michaelkamprath/eater-sap-1-improvements/advanced-alu/schematics/advanced-alu/a-register.kicad_sch

## KiCad design advanced-alu/schematics/advanced-alu/a-register.kicad_sch (2022-05-16)

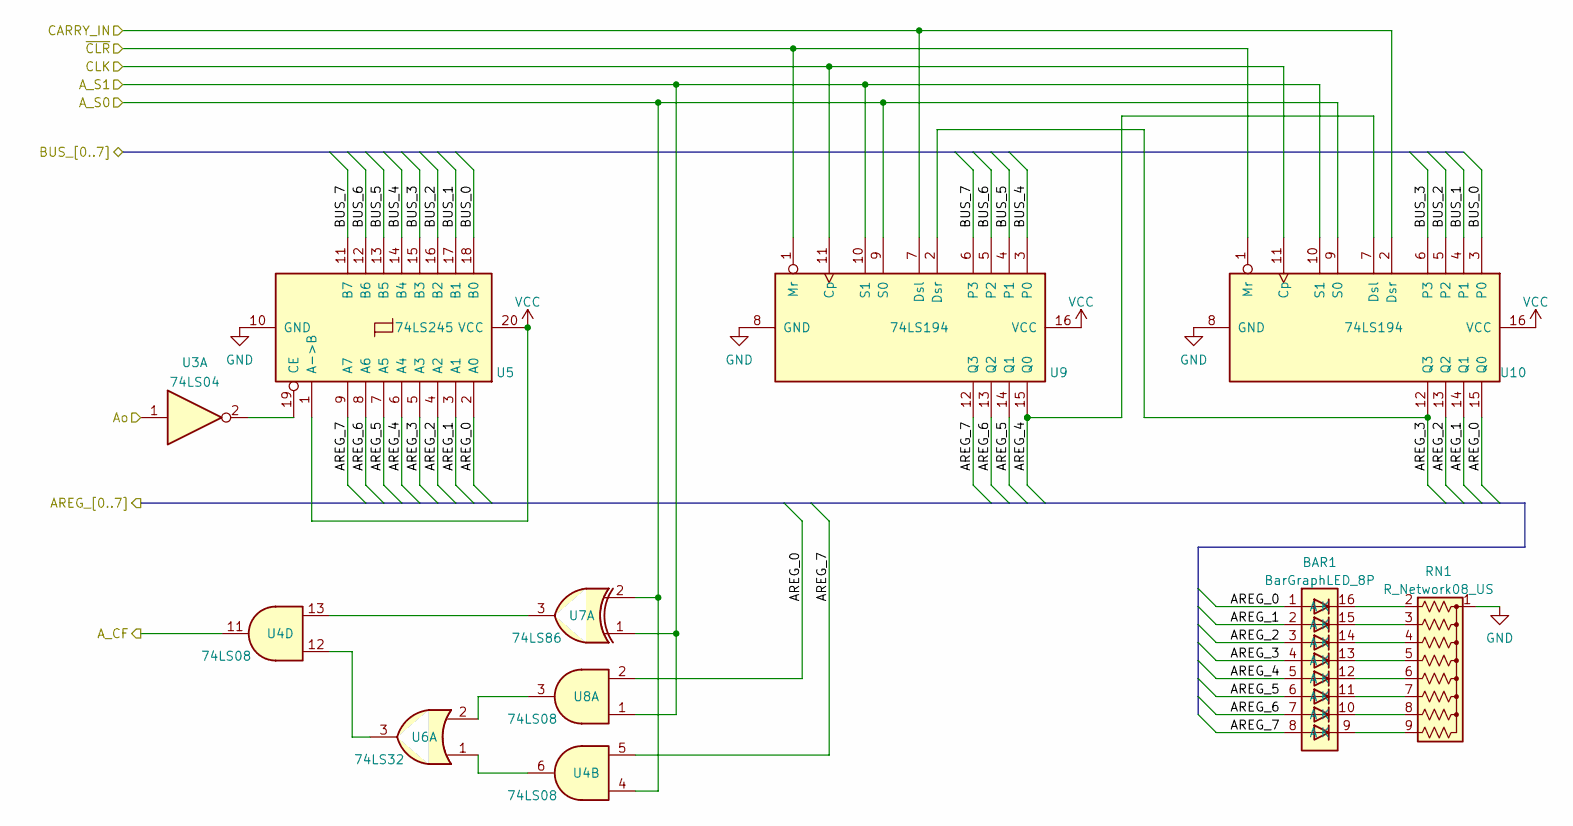
[picture p28: schematic a-register.kicad_sch]

Parts:
BAR1: BarGraphLED_8P
RN1: R_Network08_US; R_Array_SIP9
U3: 74LS04
U4, U8: 74LS08
U5: 74LS245
U6: 74LS32
U7: 74LS86
U9, U10: 74LS194

Connections:
AREG_0: BAR1.1 (A), U5.2 (A0), U8.2, U10.15 (Q0)
AREG_1: BAR1.2 (A), U5.3 (A1), U10.14 (Q1)
AREG_2: BAR1.3 (A), U5.4 (A2), U10.13 (Q2)
AREG_3: BAR1.4 (A), U5.5 (A3), U9.2 (Dsr), U10.12 (Q3)
AREG_4: BAR1.5 (A), U5.6 (A4), U9.15 (Q0), U10.7 (Dsl)
AREG_5: BAR1.6 (A), U5.7 (A5), U9.14 (Q1)
AREG_6: BAR1.7 (A), U5.8 (A6), U9.13 (Q2)
AREG_7: BAR1.8 (A), U4.5, U5.9 (A7), U9.12 (Q3)
A_CF: U4.11
A_S0: U4.4, U7.2, U9.9 (S0), U10.9 (S0)
A_S1: U7.1, U8.1, U9.10 (S1), U10.10 (S1)
Ao: U3.1
BUS_0: U5.18 (B0), U10.3 (P0)
BUS_1: U5.17 (B1), U10.4 (P1)
BUS_2: U5.16 (B2), U10.5 (P2)
BUS_3: U5.15 (B3), U10.6 (P3)
BUS_4: U5.14 (B4), U9.3 (P0)
BUS_5: U5.13 (B5), U9.4 (P1)
BUS_6: U5.12 (B6), U9.5 (P2)
BUS_7: U5.11 (B7), U9.6 (P3)
CARRY_IN: U9.7 (Dsl), U10.2 (Dsr)
CLK: U9.11 (Cp), U10.11 (Cp)
GND: RN1.1 (common), U5.10 (GND), U9.8 (GND), U10.8 (GND)
unnamed: BAR1.9 (K), RN1.9 (R8)
unnamed: BAR1.10 (K), RN1.8 (R7)
unnamed: BAR1.11 (K), RN1.7 (R6)
unnamed: BAR1.12 (K), RN1.6 (R5)
unnamed: BAR1.13 (K), RN1.5 (R4)
unnamed: BAR1.14 (K), RN1.4 (R3)
unnamed: BAR1.15 (K), RN1.3 (R2)
unnamed: BAR1.16 (K), RN1.2 (R1)
unnamed: U3.2, U5.19 (CE)
unnamed: U4.6, U6.1
unnamed: U4.12, U6.3
unnamed: U4.13, U7.3
unnamed: U6.2, U8.3
VCC: U5.1 (A->B), U5.20 (VCC), U9.16 (VCC), U10.16 (VCC)
~CLR: U9.1 (Mr), U10.1 (Mr)
