michaelkamprath/eater-sap-1-improvements/advanced-alu/schematics/advanced-alu/advanced-alu.kicad_sch

## KiCad design advanced-alu/schematics/advanced-alu/advanced-alu.kicad_sch (2022-05-16)

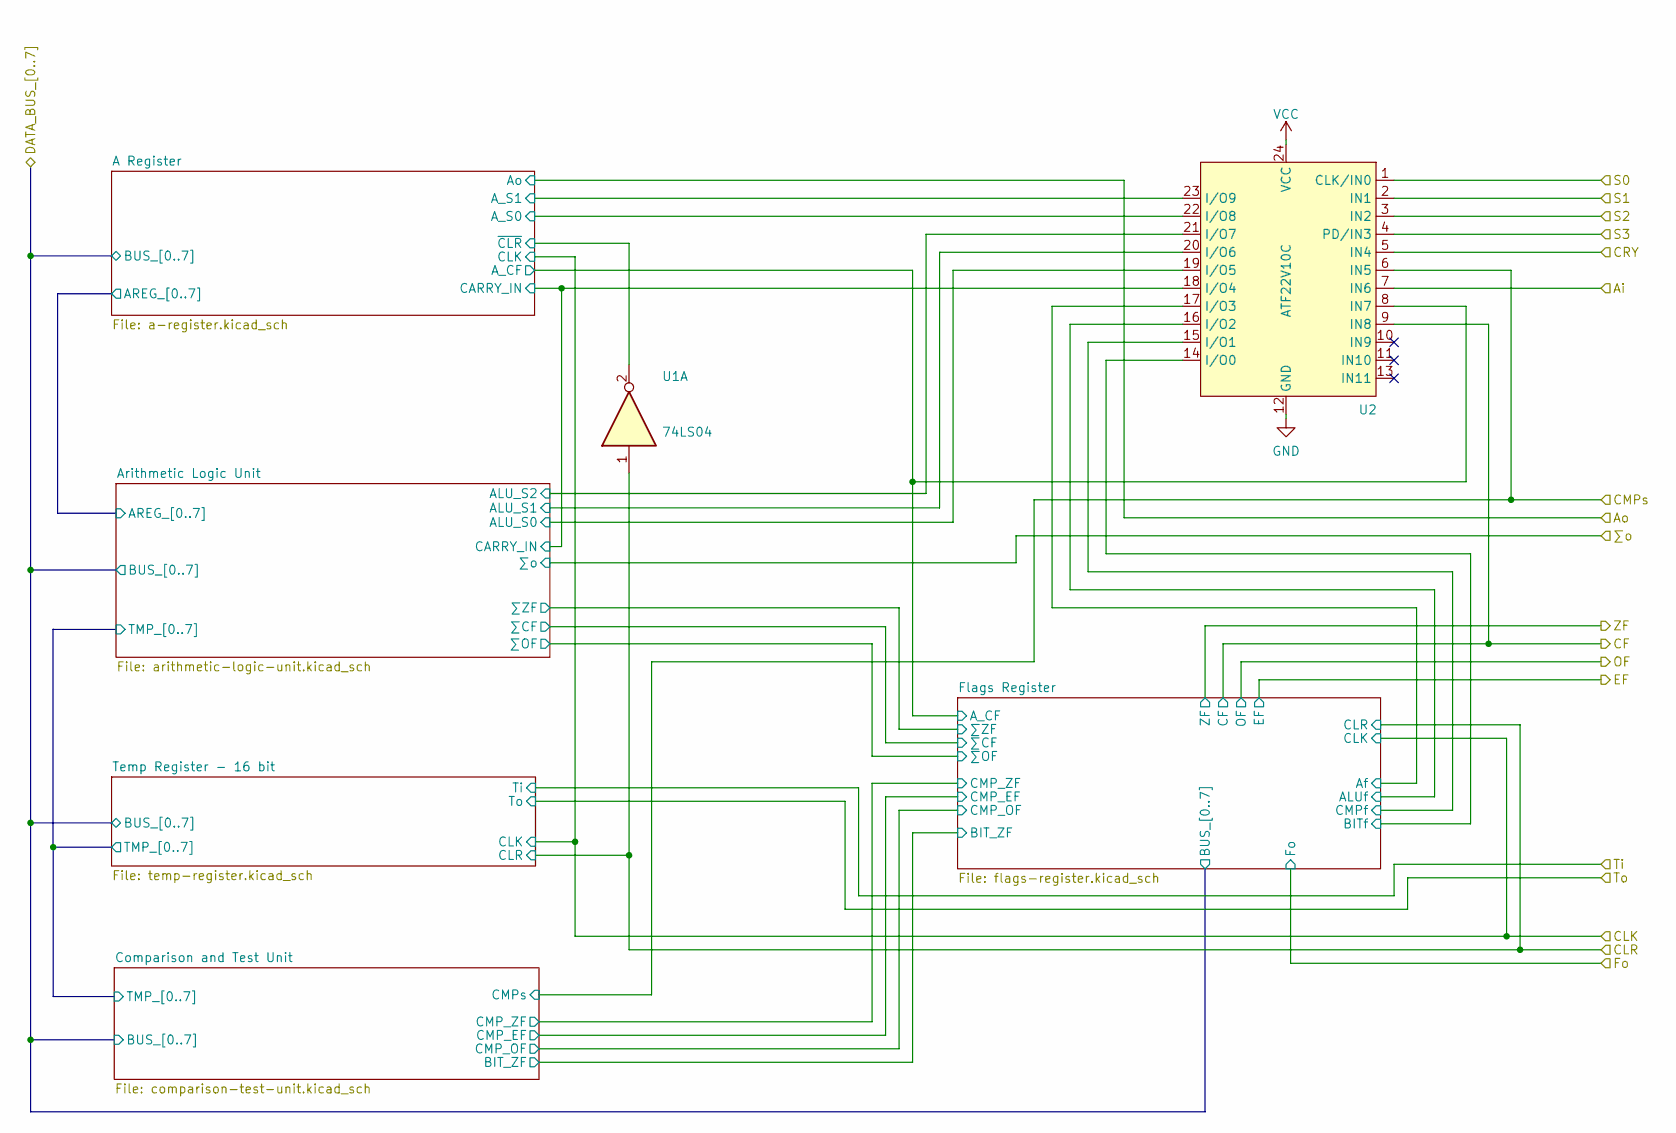
[picture p29: schematic advanced-alu.kicad_sch]

Parts:
U1: 74LS04
U2: ATF22V10C

Connections:
ALU_S0: U2.19 (I/O5)
ALU_S1: U2.20 (I/O6)
ALU_S2: U2.21 (I/O7)
ALUf: U2.16 (I/O2)
A_CF: U2.8 (IN7)
A_S0: U2.22 (I/O8)
A_S1: U2.23 (I/O9)
Af: U2.17 (I/O3)
Ai: U2.7 (IN6)
BITf: U2.14 (I/O0)
CARRY_IN: U2.18 (I/O4)
CF: U2.9 (IN8)
CLR: U1.1
CMPf: U2.15 (I/O1)
CMPs: U2.6 (IN5)
CRY: U2.5 (IN4)
GND: U2.12 (GND)
S0: U2.1 (CLK/IN0)
S1: U2.2 (IN1)
S2: U2.3 (IN2)
S3: U2.4 (PD/IN3)
VCC: U2.24 (VCC)
~CLR: U1.2
