michaelkamprath/eater-sap-1-improvements/advanced-alu/schematics/advanced-alu/arithmetic-logic-unit.kicad_sch

## KiCad design advanced-alu/schematics/advanced-alu/arithmetic-logic-unit.kicad_sch (2022-05-16)

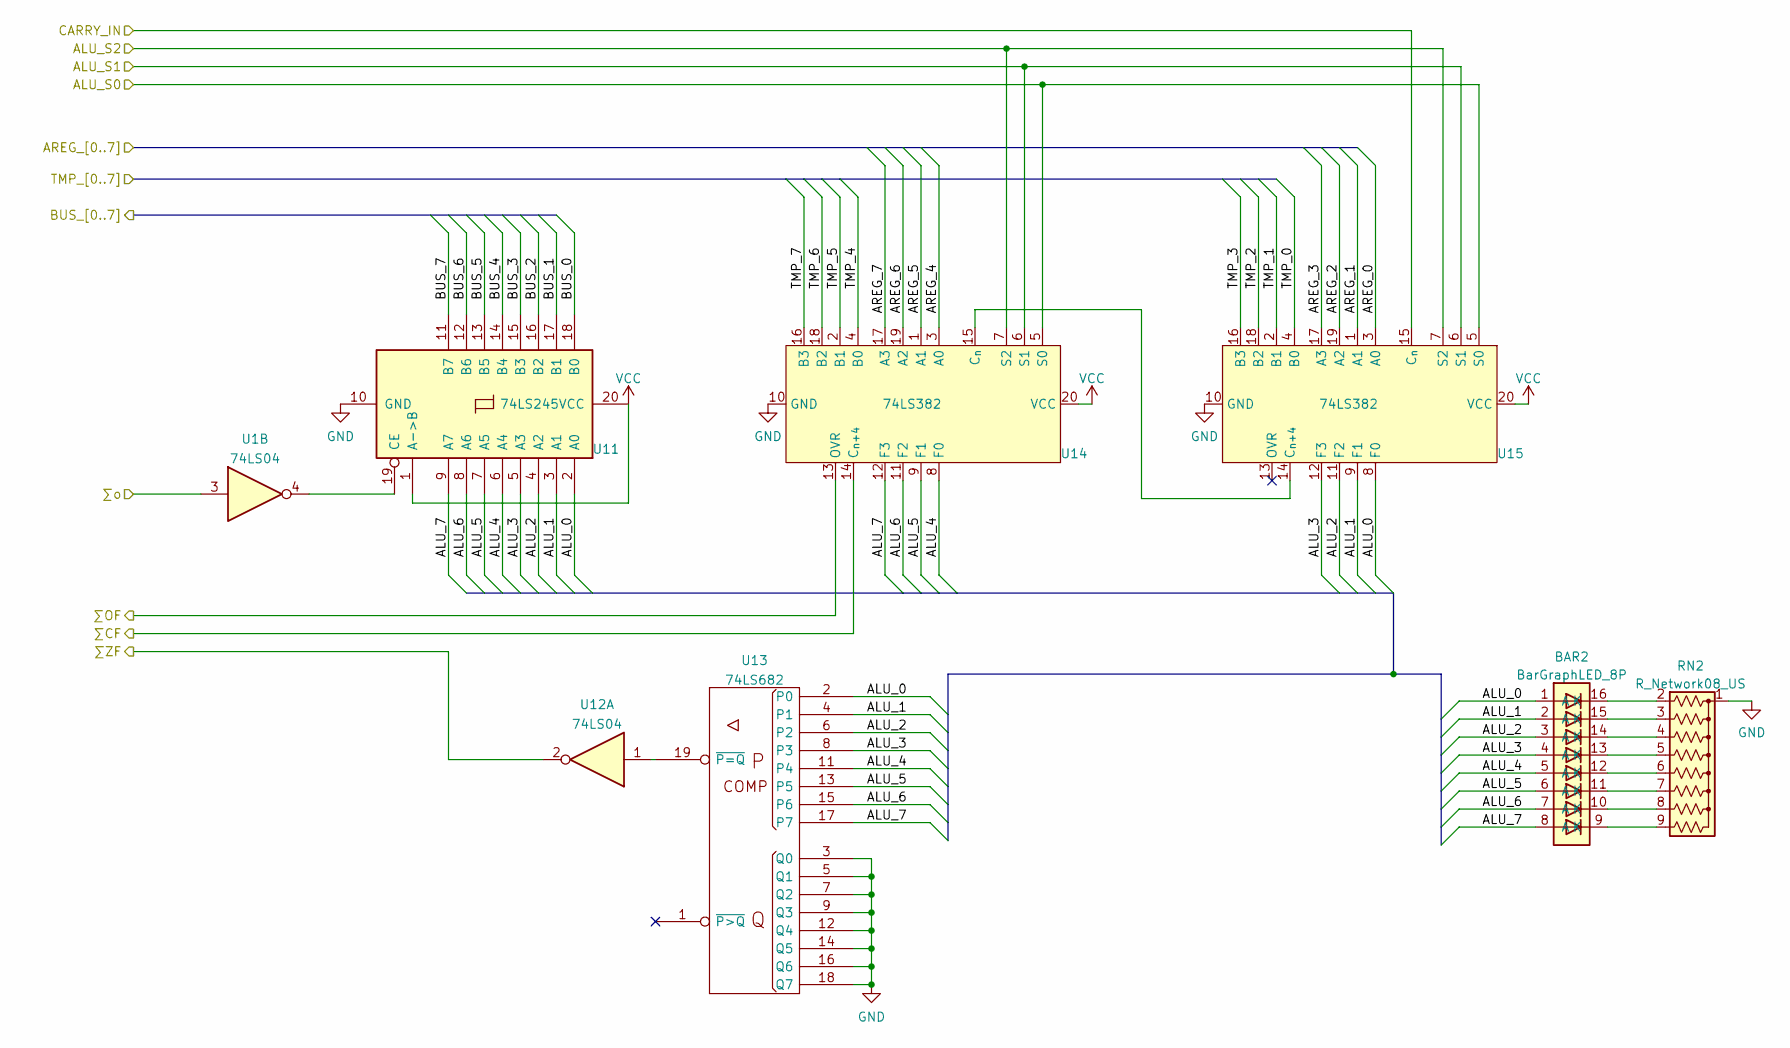
[picture p30: schematic arithmetic-logic-unit.kicad_sch]

Parts:
BAR2: BarGraphLED_8P
RN2: R_Network08_US; R_Array_SIP9
U1, U12: 74LS04
U11: 74LS245
U13: 74LS682
U14, U15: 74LS382

Connections:
ALU_0: BAR2.1 (A), U11.2 (A0), U13.2 (P0), U15.8 (F0)
ALU_1: BAR2.2 (A), U11.3 (A1), U13.4 (P1), U15.9 (F1)
ALU_2: BAR2.3 (A), U11.4 (A2), U13.6 (P2), U15.11 (F2)
ALU_3: BAR2.4 (A), U11.5 (A3), U13.8 (P3), U15.12 (F3)
ALU_4: BAR2.5 (A), U11.6 (A4), U13.11 (P4), U14.8 (F0)
ALU_5: BAR2.6 (A), U11.7 (A5), U13.13 (P5), U14.9 (F1)
ALU_6: BAR2.7 (A), U11.8 (A6), U13.15 (P6), U14.11 (F2)
ALU_7: BAR2.8 (A), U11.9 (A7), U13.17 (P7), U14.12 (F3)
ALU_S0: U14.5 (S0), U15.5 (S0)
ALU_S1: U14.6 (S1), U15.6 (S1)
ALU_S2: U14.7 (S2), U15.7 (S2)
AREG_0: U15.3 (A0)
AREG_1: U15.1 (A1)
AREG_2: U15.19 (A2)
AREG_3: U15.17 (A3)
AREG_4: U14.3 (A0)
AREG_5: U14.1 (A1)
AREG_6: U14.19 (A2)
AREG_7: U14.17 (A3)
BUS_0: U11.18 (B0)
BUS_1: U11.17 (B1)
BUS_2: U11.16 (B2)
BUS_3: U11.15 (B3)
BUS_4: U11.14 (B4)
BUS_5: U11.13 (B5)
BUS_6: U11.12 (B6)
BUS_7: U11.11 (B7)
CARRY_IN: U15.15 (C_{n})
GND: RN2.1 (common), U11.10 (GND), U13.3 (Q0), U13.5 (Q1), U13.7 (Q2), U13.9 (Q3), U13.12 (Q4), U13.14 (Q5), U13.16 (Q6), U13.18 (Q7), U14.10 (GND), U15.10 (GND)
unnamed: BAR2.9 (K), RN2.9 (R8)
unnamed: BAR2.10 (K), RN2.8 (R7)
unnamed: BAR2.11 (K), RN2.7 (R6)
unnamed: BAR2.12 (K), RN2.6 (R5)
unnamed: BAR2.13 (K), RN2.5 (R4)
unnamed: BAR2.14 (K), RN2.4 (R3)
unnamed: BAR2.15 (K), RN2.3 (R2)
unnamed: BAR2.16 (K), RN2.2 (R1)
unnamed: U1.4, U11.19 (CE)
unnamed: U12.1, U13.19 (~P=Q)
unnamed: U14.15 (C_{n}), U15.14 (C_{n+4})
TMP_0: U15.4 (B0)
TMP_1: U15.2 (B1)
TMP_2: U15.18 (B2)
TMP_3: U15.16 (B3)
TMP_4: U14.4 (B0)
TMP_5: U14.2 (B1)
TMP_6: U14.18 (B2)
TMP_7: U14.16 (B3)
VCC: U11.1 (A->B), U11.20 (VCC), U14.20 (VCC), U15.20 (VCC)
∑CF: U14.14 (C_{n+4})
∑OF: U14.13 (OVR)
∑ZF: U12.2
∑o: U1.3
