michaelkamprath/eater-sap-1-improvements/advanced-alu/schematics/advanced-alu/temp-register.kicad_sch

## KiCad design advanced-alu/schematics/advanced-alu/temp-register.kicad_sch (2022-05-16)

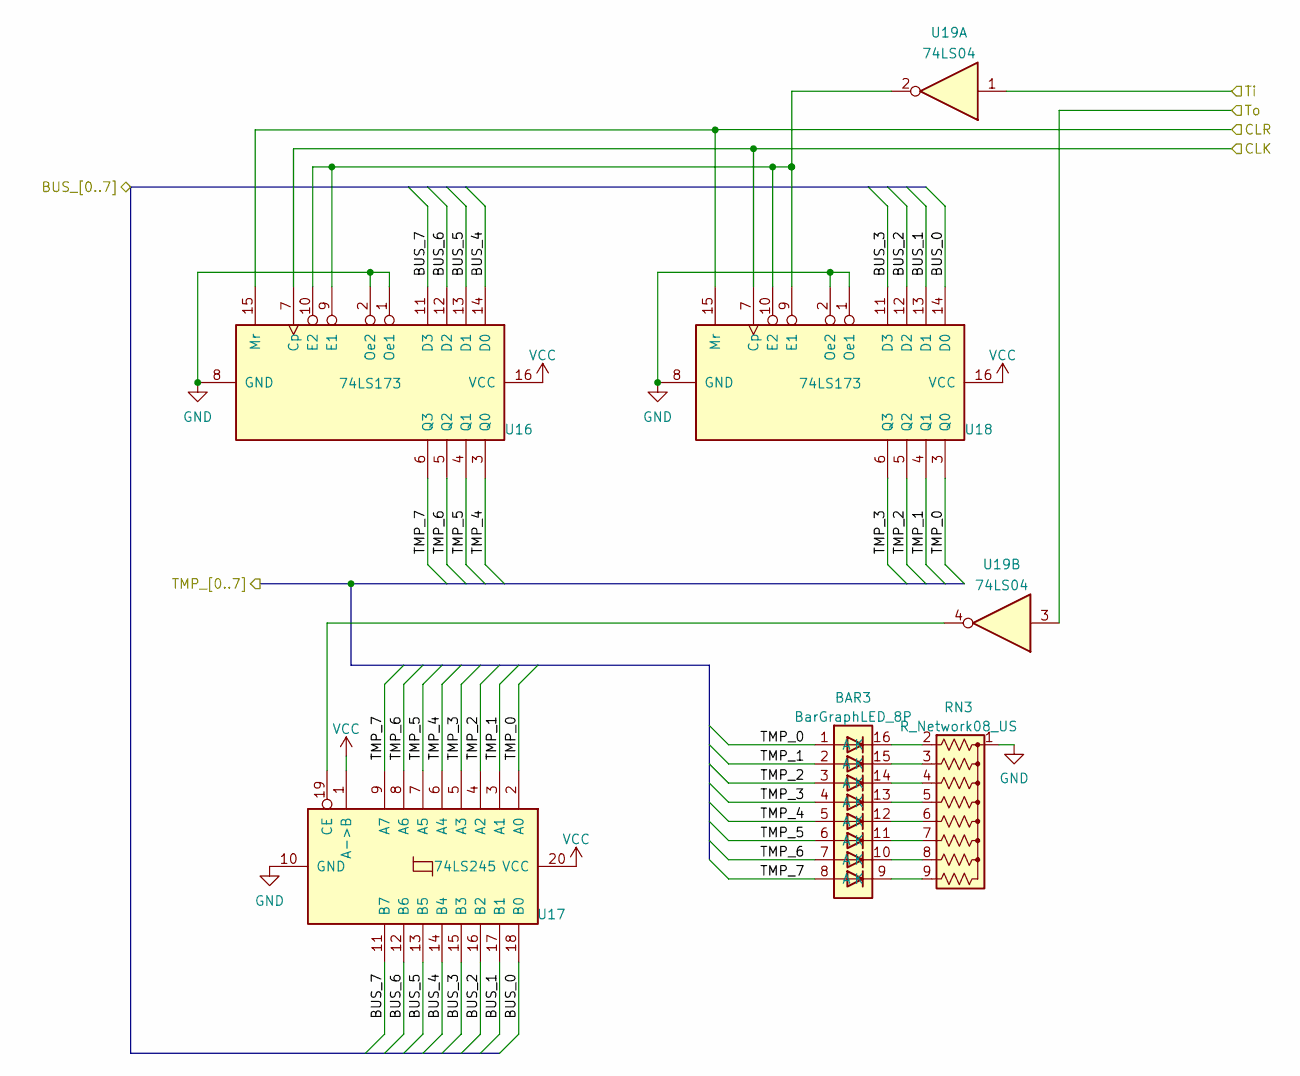
[picture p33: schematic temp-register.kicad_sch]

Parts:
BAR3: BarGraphLED_8P
RN3: R_Network08_US; R_Array_SIP9
U16, U18: 74LS173
U17: 74LS245
U19: 74LS04

Connections:
BUS_0: U17.18 (B0), U18.14 (D0)
BUS_1: U17.17 (B1), U18.13 (D1)
BUS_2: U17.16 (B2), U18.12 (D2)
BUS_3: U17.15 (B3), U18.11 (D3)
BUS_4: U16.14 (D0), U17.14 (B4)
BUS_5: U16.13 (D1), U17.13 (B5)
BUS_6: U16.12 (D2), U17.12 (B6)
BUS_7: U16.11 (D3), U17.11 (B7)
CLK: U16.7 (Cp), U18.7 (Cp)
CLR: U16.15 (Mr), U18.15 (Mr)
GND: RN3.1 (common), U16.1 (Oe1), U16.2 (Oe2), U16.8 (GND), U17.10 (GND), U18.1 (Oe1), U18.2 (Oe2), U18.8 (GND)
unnamed: BAR3.9 (K), RN3.9 (R8)
unnamed: BAR3.10 (K), RN3.8 (R7)
unnamed: BAR3.11 (K), RN3.7 (R6)
unnamed: BAR3.12 (K), RN3.6 (R5)
unnamed: BAR3.13 (K), RN3.5 (R4)
unnamed: BAR3.14 (K), RN3.4 (R3)
unnamed: BAR3.15 (K), RN3.3 (R2)
unnamed: BAR3.16 (K), RN3.2 (R1)
unnamed: U16.9 (E1), U16.10 (E2), U18.9 (E1), U18.10 (E2), U19.2
unnamed: U17.19 (CE), U19.4
TMP_0: BAR3.1 (A), U17.2 (A0), U18.3 (Q0)
TMP_1: BAR3.2 (A), U17.3 (A1), U18.4 (Q1)
TMP_2: BAR3.3 (A), U17.4 (A2), U18.5 (Q2)
TMP_3: BAR3.4 (A), U17.5 (A3), U18.6 (Q3)
TMP_4: BAR3.5 (A), U16.3 (Q0), U17.6 (A4)
TMP_5: BAR3.6 (A), U16.4 (Q1), U17.7 (A5)
TMP_6: BAR3.7 (A), U16.5 (Q2), U17.8 (A6)
TMP_7: BAR3.8 (A), U16.6 (Q3), U17.9 (A7)
Ti: U19.1
To: U19.3
VCC: U16.16 (VCC), U17.1 (A->B), U17.20 (VCC), U18.16 (VCC)
