michaelkamprath/eater-sap-1-improvements/advanced-alu/schematics/instruction-register-step-counter/instruction-register-step-counter.kicad_sch

## KiCad design advanced-alu/schematics/instruction-register-step-counter/instruction-register-step-counter.kicad_sch (2022-05-16)

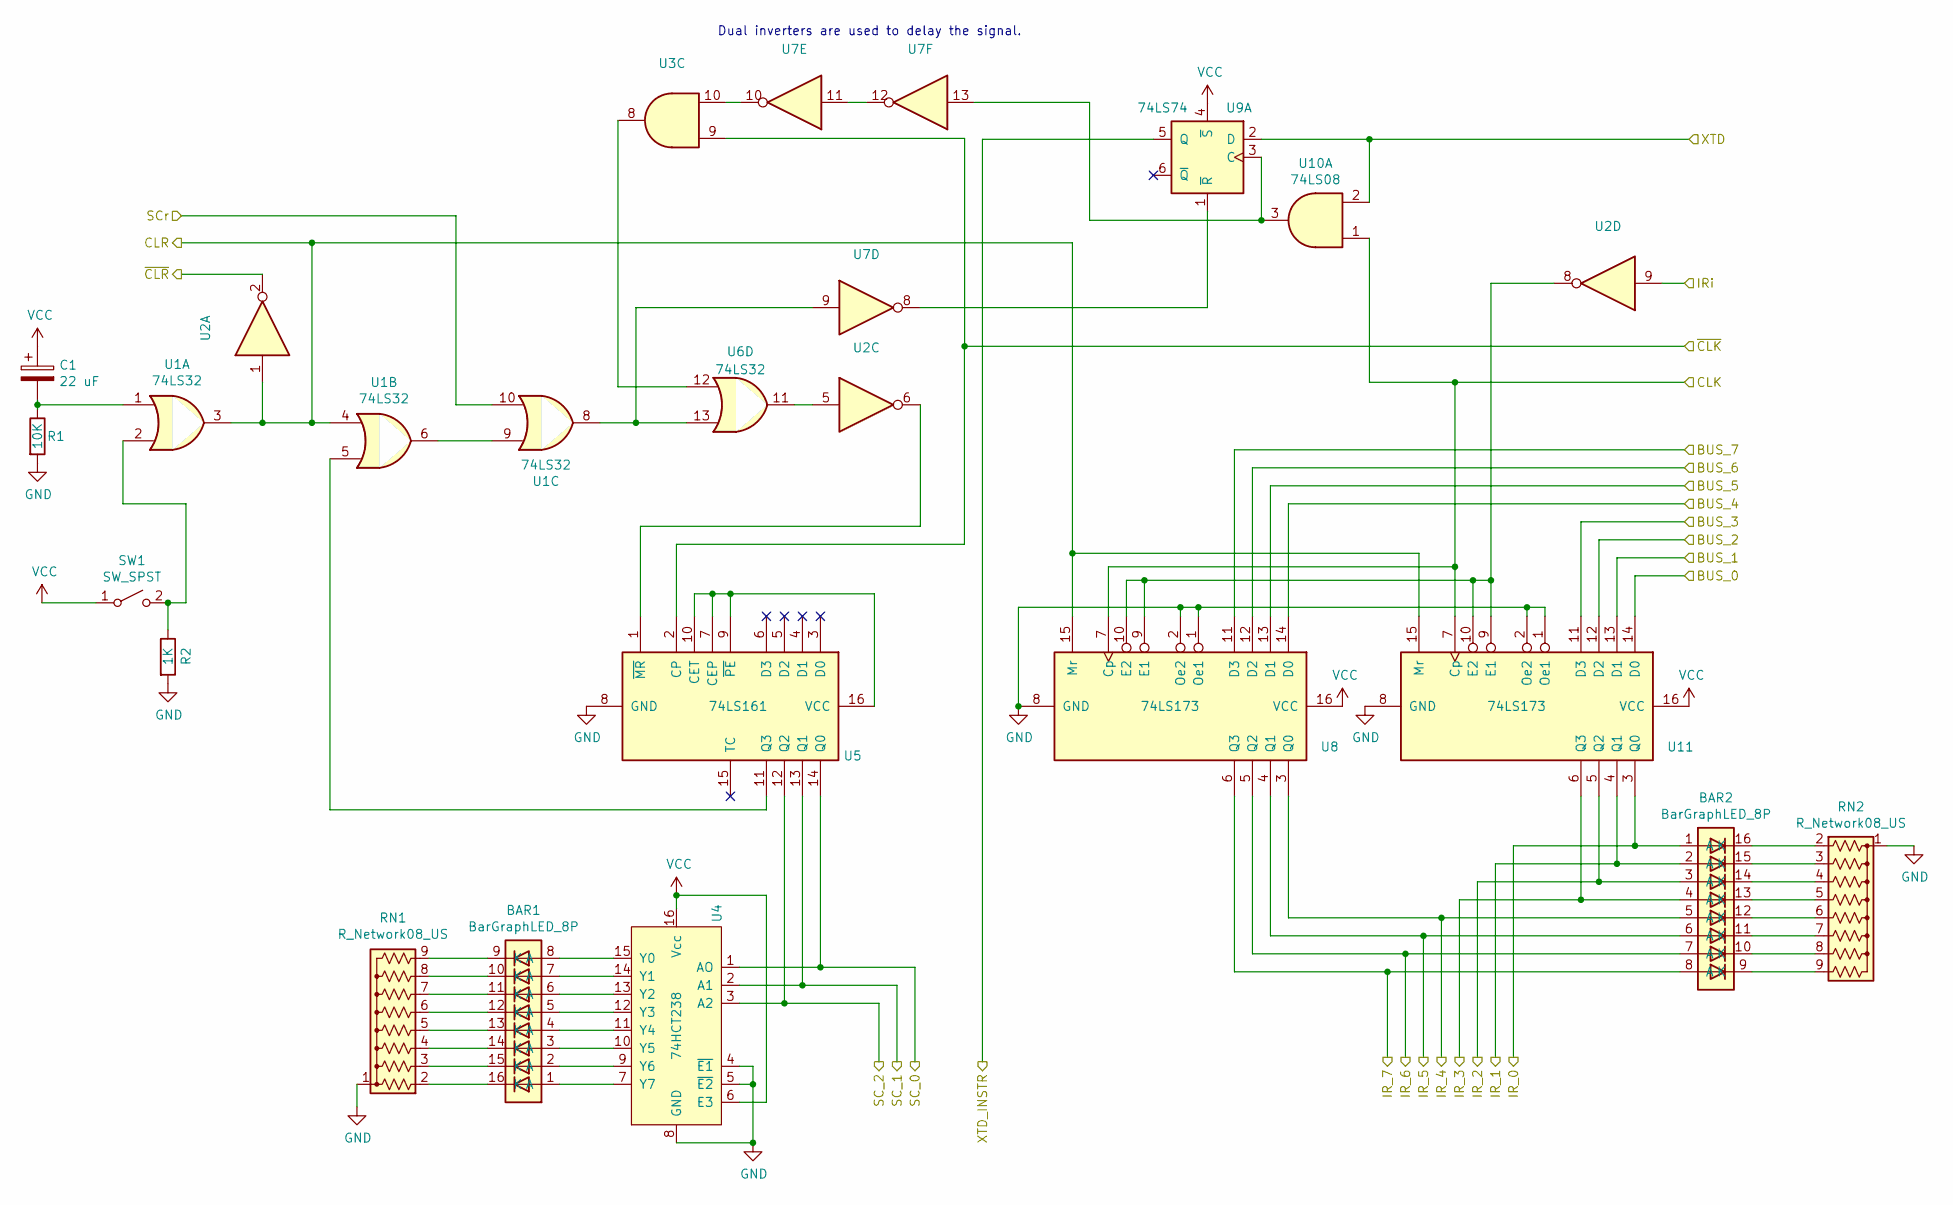
[picture p35: schematic instruction-register-step-counter.kicad_sch]

Parts:
BAR1, BAR2: BarGraphLED_8P
C1: 22 uF
R1: 10K
R2: 1K
RN1, RN2: R_Network08_US; R_Array_SIP9
SW1: SW_SPST
U1, U6: 74LS32
U2, U3, U7: (no value)
U4: 74HCT238
U5: 74LS161
U8, U11: 74LS173
U9: 74LS74
U10: 74LS08

Connections:
BUS_0: U11.14 (D0)
BUS_1: U11.13 (D1)
BUS_2: U11.12 (D2)
BUS_3: U11.11 (D3)
BUS_4: U8.14 (D0)
BUS_5: U8.13 (D1)
BUS_6: U8.12 (D2)
BUS_7: U8.11 (D3)
CLK: U8.7 (Cp), U10.1, U11.7 (Cp)
CLR: U1.3, U1.4, U2.1, U8.15 (Mr), U11.15 (Mr)
GND: R1.2, R2.2, RN1.1 (common), RN2.1 (common), U4.4 (~E1), U4.5 (~E2), U4.8 (GND), U5.8 (GND), U8.1 (Oe1), U8.2 (Oe2), U8.8 (GND), U11.1 (Oe1), U11.2 (Oe2), U11.8 (GND)
IR_0: BAR2.1 (A), U11.3 (Q0)
IR_1: BAR2.2 (A), U11.4 (Q1)
IR_2: BAR2.3 (A), U11.5 (Q2)
IR_3: BAR2.4 (A), U11.6 (Q3)
IR_4: BAR2.5 (A), U8.3 (Q0)
IR_5: BAR2.6 (A), U8.4 (Q1)
IR_6: BAR2.7 (A), U8.5 (Q2)
IR_7: BAR2.8 (A), U8.6 (Q3)
IRi: U2.9
unnamed: BAR1.1 (A), U4.7 (Y7)
unnamed: BAR1.2 (A), U4.9 (Y6)
unnamed: BAR1.3 (A), U4.10 (Y5)
unnamed: BAR1.4 (A), U4.11 (Y4)
unnamed: BAR1.5 (A), U4.12 (Y3)
unnamed: BAR1.6 (A), U4.13 (Y2)
unnamed: BAR1.7 (A), U4.14 (Y1)
unnamed: BAR1.8 (A), U4.15 (Y0)
unnamed: BAR1.9 (K), RN1.9 (R8)
unnamed: BAR1.10 (K), RN1.8 (R7)
unnamed: BAR1.11 (K), RN1.7 (R6)
unnamed: BAR1.12 (K), RN1.6 (R5)
unnamed: BAR1.13 (K), RN1.5 (R4)
unnamed: BAR1.14 (K), RN1.4 (R3)
unnamed: BAR1.15 (K), RN1.3 (R2)
unnamed: BAR1.16 (K), RN1.2 (R1)
unnamed: BAR2.9 (K), RN2.9 (R8)
unnamed: BAR2.10 (K), RN2.8 (R7)
unnamed: BAR2.11 (K), RN2.7 (R6)
unnamed: BAR2.12 (K), RN2.6 (R5)
unnamed: BAR2.13 (K), RN2.5 (R4)
unnamed: BAR2.14 (K), RN2.4 (R3)
unnamed: BAR2.15 (K), RN2.3 (R2)
unnamed: BAR2.16 (K), RN2.2 (R1)
unnamed: C1.2, R1.1, U1.1
unnamed: R2.1, SW1.2 (B), U1.2
unnamed: U1.5, U5.11 (Q3)
unnamed: U1.6, U1.9
unnamed: U1.8, U6.13, U7.9
unnamed: U2.5, U6.11
unnamed: U2.6, U5.1 (~MR)
unnamed: U3.8, U6.12
unnamed: U3.10, U7.10
unnamed: U5.7 (CEP), U5.9 (~PE), U5.10 (CET), U5.16 (VCC)
unnamed: U7.8, U9.1 (~R)
unnamed: U7.11, U7.12
unnamed: U7.13, U9.3 (C), U10.3
unnamed: U2.8, U8.9 (E1), U8.10 (E2), U11.9 (E1), U11.10 (E2)
SC_0: U4.1 (AO), U5.14 (Q0)
SC_1: U4.2 (A1), U5.13 (Q1)
SC_2: U4.3 (A2), U5.12 (Q2)
SCr: U1.10
VCC: C1.1, SW1.1 (A), U4.6 (E3), U4.16 (Vcc), U8.16 (VCC), U9.4 (~S), U11.16 (VCC)
XTD: U9.2 (D), U10.2
XTD_INSTR: U9.5 (Q)
~CLK: U3.9, U5.2 (CP)
~CLR: U2.2

Notes on the sheet:
Dual inverters are used to delay the signal.
