michaelkamprath/eater-sap-1-improvements/advanced-alu/schematics/memory-map-controller/memory-map-controller.kicad_sch

## KiCad design advanced-alu/schematics/memory-map-controller/memory-map-controller.kicad_sch (2022-05-28)

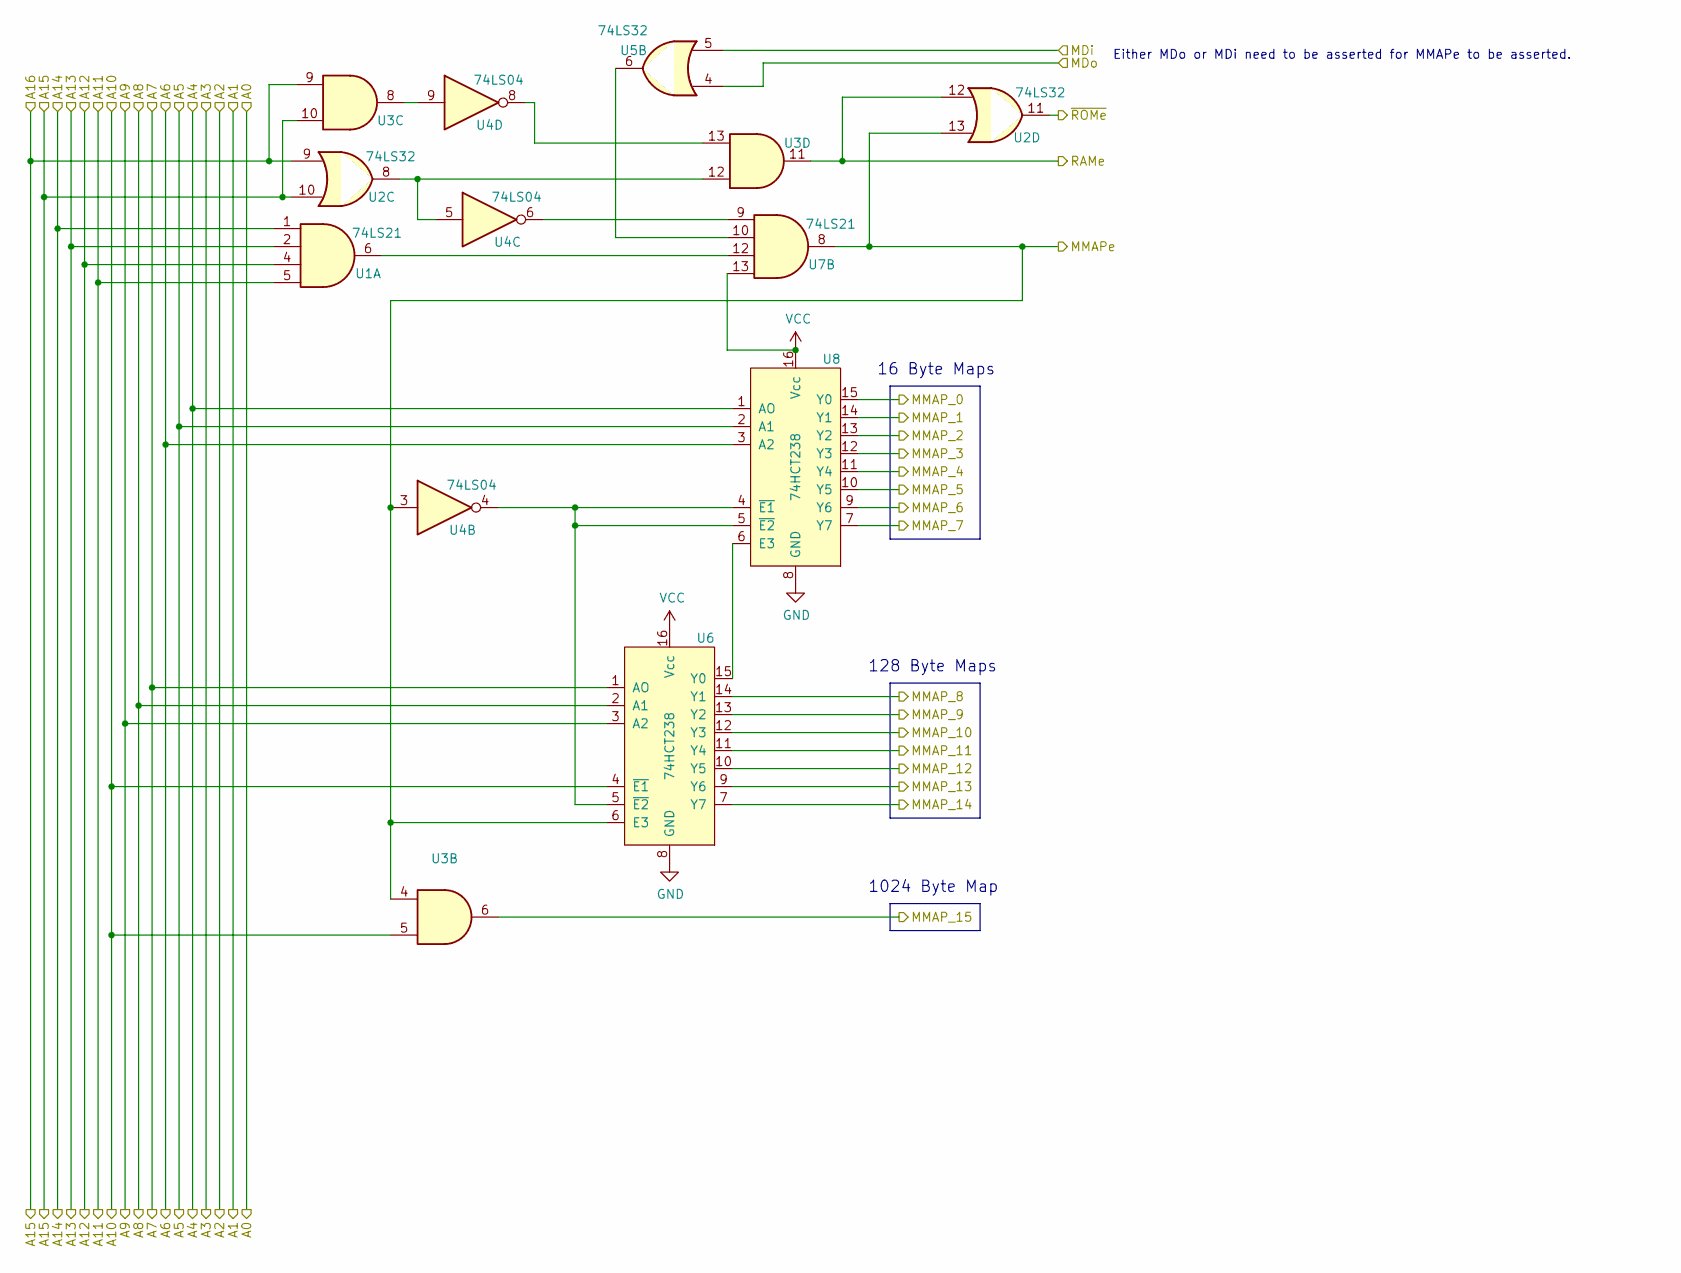
[picture p36: schematic memory-map-controller.kicad_sch]

Parts:
U1, U7: 74LS21
U2, U5: 74LS32
U3: (no value)
U4: 74LS04
U6, U8: 74HCT238

Connections:
A4: U8.1 (AO)
A5: U8.2 (A1)
A6: U8.3 (A2)
A7: U6.1 (AO)
A8: U6.2 (A1)
A9: U6.3 (A2)
A10: U3.5, U6.4 (~E1)
A11: U1.5
A12: U1.4
A13: U1.2
A14: U1.1
A15: U2.9, U2.10, U3.9, U3.10
GND: U6.8 (GND), U8.8 (GND)
MDi: U5.5
MDo: U5.4
MMAP_0: U8.15 (Y0)
MMAP_1: U8.14 (Y1)
MMAP_2: U8.13 (Y2)
MMAP_3: U8.12 (Y3)
MMAP_4: U8.11 (Y4)
MMAP_5: U8.10 (Y5)
MMAP_6: U8.9 (Y6)
MMAP_7: U8.7 (Y7)
MMAP_8: U6.14 (Y1)
MMAP_9: U6.13 (Y2)
MMAP_10: U6.12 (Y3)
MMAP_11: U6.11 (Y4)
MMAP_12: U6.10 (Y5)
MMAP_13: U6.9 (Y6)
MMAP_14: U6.7 (Y7)
MMAP_15: U3.6
MMAPe: U2.13, U3.4, U4.3, U6.6 (E3), U7.8
unnamed: U1.6, U7.12
unnamed: U2.8, U3.12, U4.5
unnamed: U3.8, U4.9
unnamed: U3.13, U4.8
unnamed: U4.4, U6.5 (~E2), U8.4 (~E1), U8.5 (~E2)
unnamed: U4.6, U7.9
unnamed: U5.6, U7.10
unnamed: U6.15 (Y0), U8.6 (E3)
RAMe: U2.12, U3.11
VCC: U6.16 (Vcc), U7.13, U8.16 (Vcc)
~ROMe: U2.11

Notes on the sheet:
128 Byte Maps
1024 Byte Map
Either MDo or MDi need to be asserted for MMAPe to be asserted.
16 Byte Maps
