michaelkamprath/eater-sap-1-improvements/increment-registers/schematics/flags-register/flags-register.sch

## KiCad design increment-registers/schematics/flags-register/flags-register.sch (2021-02-28)

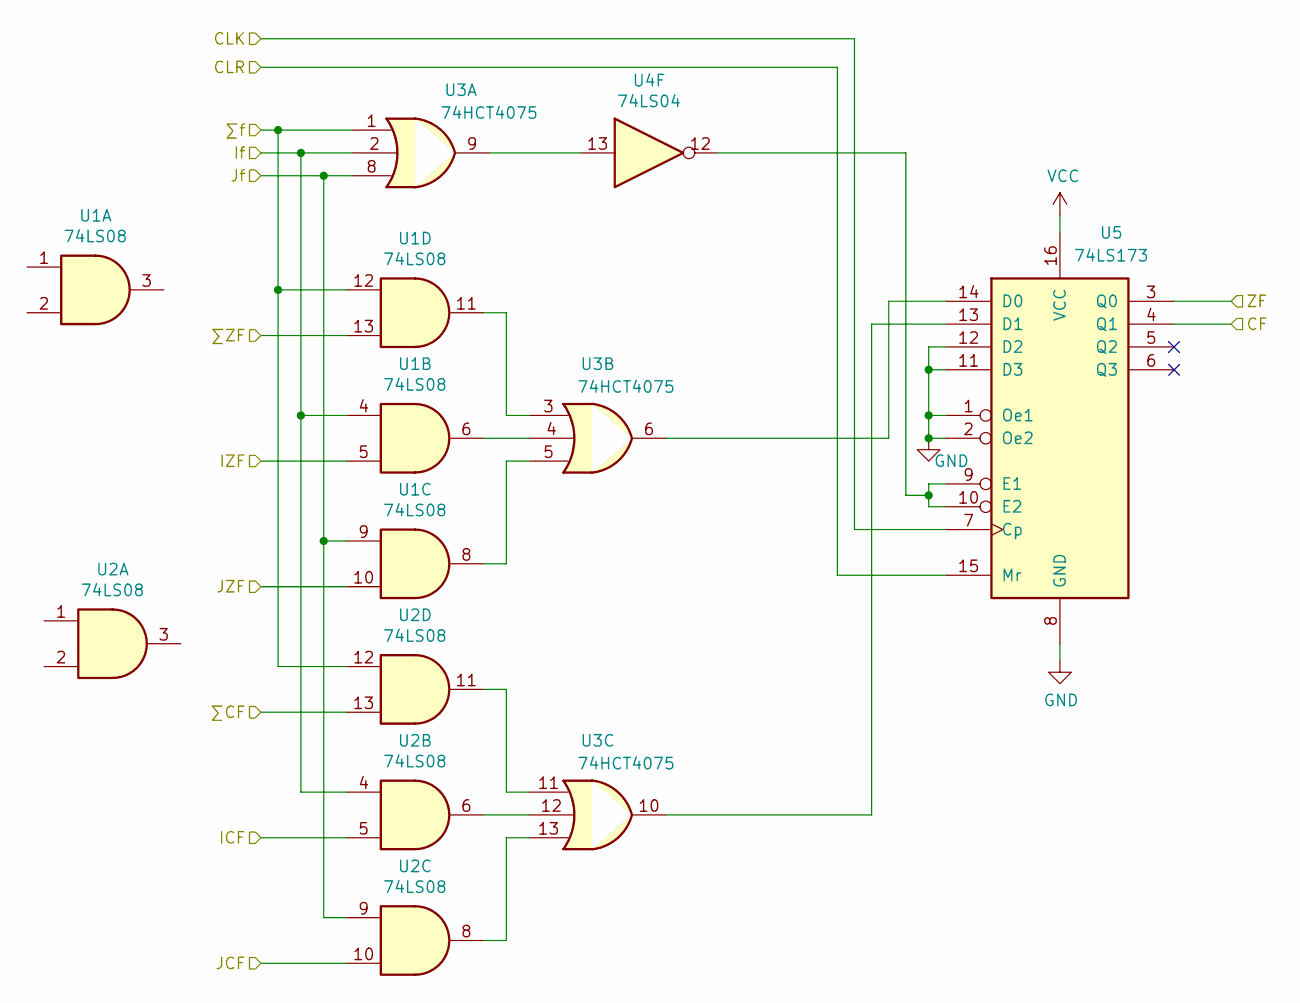
[picture p39: schematic flags-register.sch]

Parts:
U1, U2: 74LS08
U3: 74HCT4075
U4: 74LS04
U5: 74LS173

Connections:
CF: U5.4 (Q1)
CLK: U5.7 (Cp)
CLR: U5.15 (Mr)
GND: U5.1 (Oe1), U5.2 (Oe2), U5.8 (GND), U5.11 (D3), U5.12 (D2)
ICF: U2.5
IZF: U1.5
If: U1.4, U2.4, U3.2
JCF: U2.10
JZF: U1.10
Jf: U1.9, U2.9, U3.8
unnamed: U1.6, U3.4
unnamed: U1.8, U3.5
unnamed: U1.11, U3.3
unnamed: U2.6, U3.12
unnamed: U2.8, U3.13
unnamed: U2.11, U3.11
unnamed: U3.6, U5.14 (D0)
unnamed: U3.9, U4.13
unnamed: U3.10, U5.13 (D1)
unnamed: U4.12, U5.9 (E1), U5.10 (E2)
VCC: U5.16 (VCC)
ZF: U5.3 (Q0)
∑CF: U2.13
∑ZF: U1.13
∑f: U1.12, U2.12, U3.1
