michaelkamprath/eater-sap-1-improvements/instruction-register-8-bit/schematics/instruction-register-step-counter/instruction-register-step-counter.kicad_sch

## KiCad design instruction-register-8-bit/schematics/instruction-register-step-counter/instruction-register-step-counter.kicad_sch (2022-12-26)

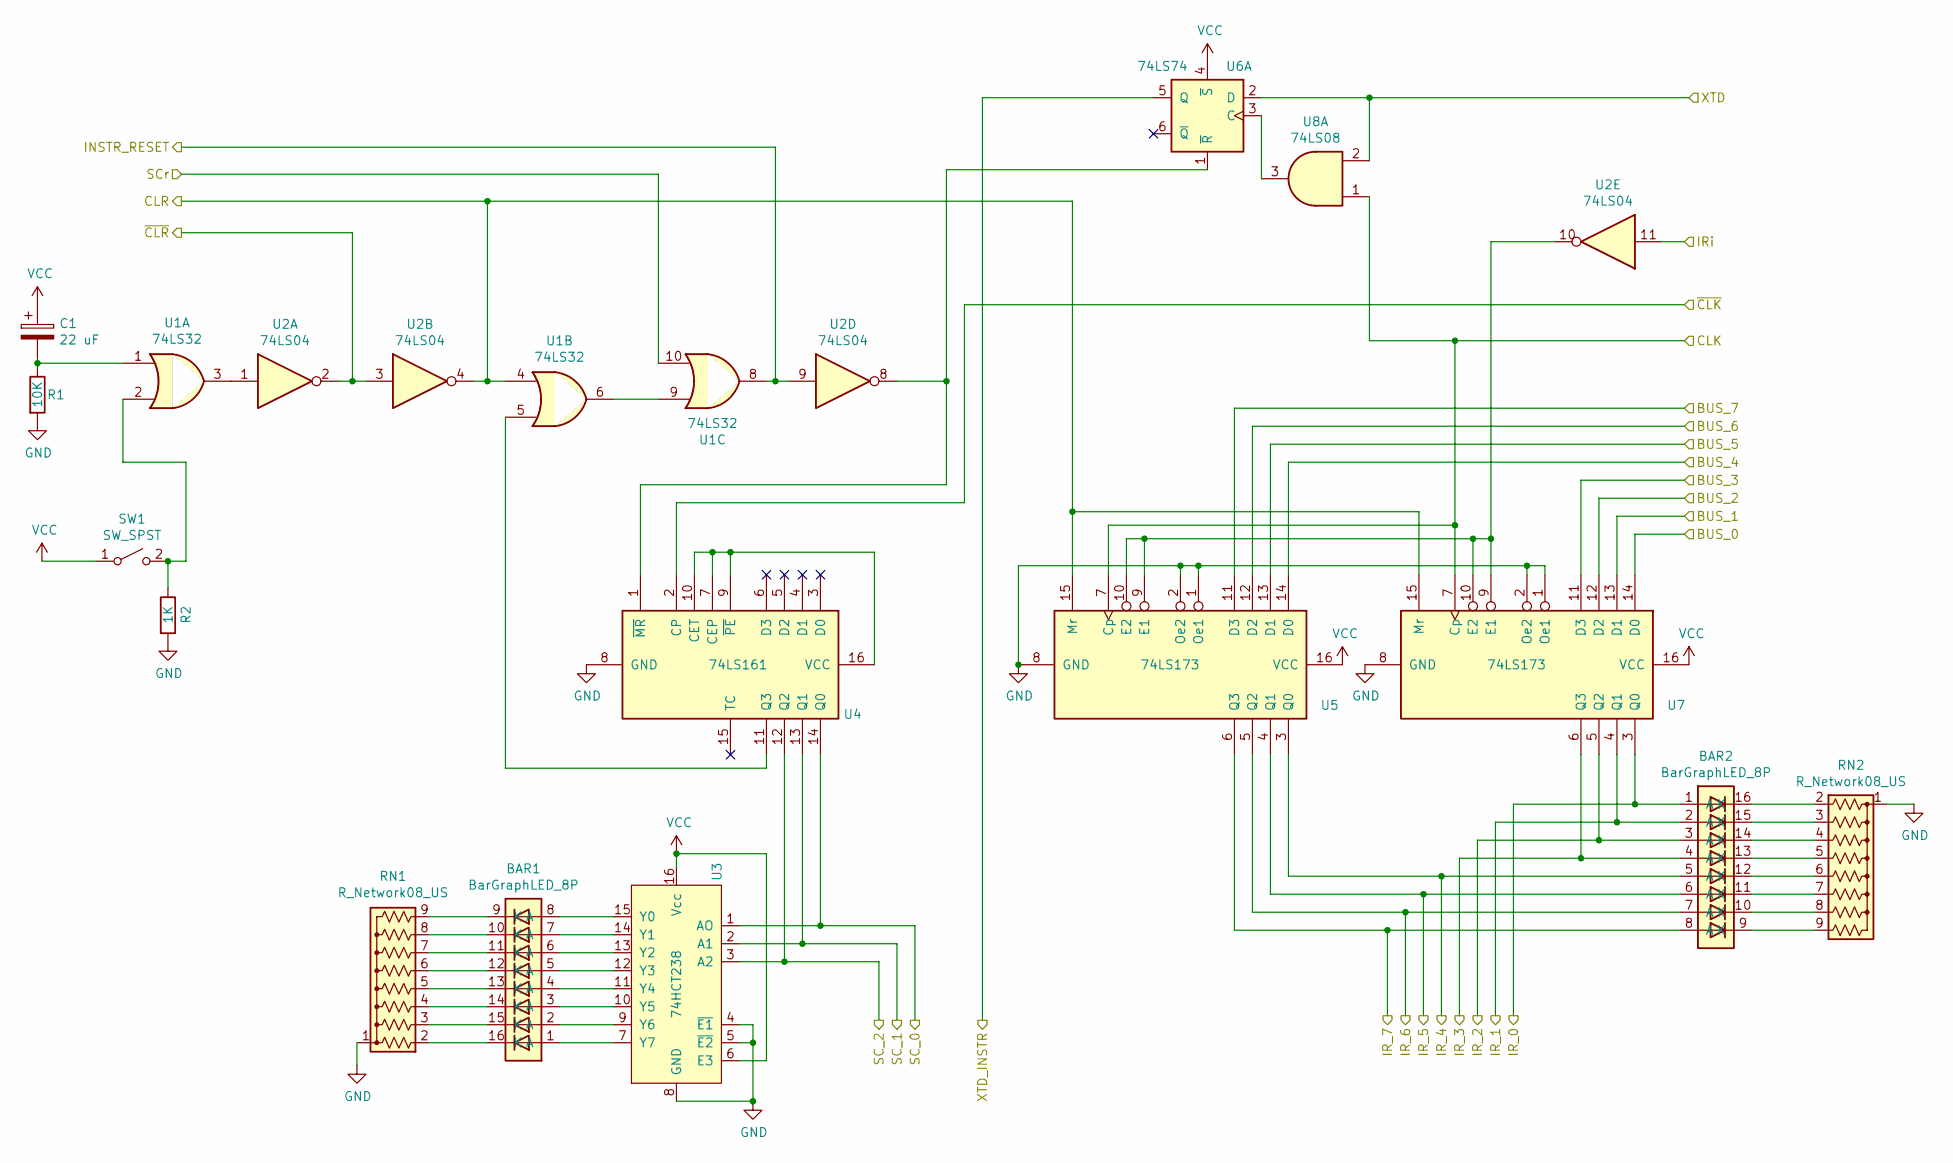
[picture p40: schematic instruction-register-step-counter.kicad_sch]

Parts:
BAR1, BAR2: BarGraphLED_8P
C1: 22 uF
R1: 10K
R2: 1K
RN1, RN2: R_Network08_US; R_Array_SIP9
SW1: SW_SPST
U1: 74LS32
U2: 74LS04
U3: 74HCT238
U4: 74LS161
U5, U7: 74LS173
U6: 74LS74
U8: 74LS08

Connections:
BUS_0: U7.14 (D0)
BUS_1: U7.13 (D1)
BUS_2: U7.12 (D2)
BUS_3: U7.11 (D3)
BUS_4: U5.14 (D0)
BUS_5: U5.13 (D1)
BUS_6: U5.12 (D2)
BUS_7: U5.11 (D3)
CLK: U5.7 (Cp), U7.7 (Cp), U8.1
CLR: U1.4, U2.4, U5.15 (Mr), U7.15 (Mr)
GND: R1.2, R2.2, RN1.1 (common), RN2.1 (common), U3.4 (~E1), U3.5 (~E2), U3.8 (GND), U4.8 (GND), U5.1 (Oe1), U5.2 (Oe2), U5.8 (GND), U7.1 (Oe1), U7.2 (Oe2), U7.8 (GND)
INSTR_RESET: U1.8, U2.9
IR_0: BAR2.1 (A), U7.3 (Q0)
IR_1: BAR2.2 (A), U7.4 (Q1)
IR_2: BAR2.3 (A), U7.5 (Q2)
IR_3: BAR2.4 (A), U7.6 (Q3)
IR_4: BAR2.5 (A), U5.3 (Q0)
IR_5: BAR2.6 (A), U5.4 (Q1)
IR_6: BAR2.7 (A), U5.5 (Q2)
IR_7: BAR2.8 (A), U5.6 (Q3)
IRi: U2.11
unnamed: BAR1.1 (A), U3.7 (Y7)
unnamed: BAR1.2 (A), U3.9 (Y6)
unnamed: BAR1.3 (A), U3.10 (Y5)
unnamed: BAR1.4 (A), U3.11 (Y4)
unnamed: BAR1.5 (A), U3.12 (Y3)
unnamed: BAR1.6 (A), U3.13 (Y2)
unnamed: BAR1.7 (A), U3.14 (Y1)
unnamed: BAR1.8 (A), U3.15 (Y0)
unnamed: BAR1.9 (K), RN1.9 (R8)
unnamed: BAR1.10 (K), RN1.8 (R7)
unnamed: BAR1.11 (K), RN1.7 (R6)
unnamed: BAR1.12 (K), RN1.6 (R5)
unnamed: BAR1.13 (K), RN1.5 (R4)
unnamed: BAR1.14 (K), RN1.4 (R3)
unnamed: BAR1.15 (K), RN1.3 (R2)
unnamed: BAR1.16 (K), RN1.2 (R1)
unnamed: BAR2.9 (K), RN2.9 (R8)
unnamed: BAR2.10 (K), RN2.8 (R7)
unnamed: BAR2.11 (K), RN2.7 (R6)
unnamed: BAR2.12 (K), RN2.6 (R5)
unnamed: BAR2.13 (K), RN2.5 (R4)
unnamed: BAR2.14 (K), RN2.4 (R3)
unnamed: BAR2.15 (K), RN2.3 (R2)
unnamed: BAR2.16 (K), RN2.2 (R1)
unnamed: C1.2, R1.1, U1.1
unnamed: R2.1, SW1.2 (B), U1.2
unnamed: U1.3, U2.1
unnamed: U1.5, U4.11 (Q3)
unnamed: U1.6, U1.9
unnamed: U2.8, U4.1 (~MR), U6.1 (~R)
unnamed: U2.10, U5.9 (E1), U5.10 (E2), U7.9 (E1), U7.10 (E2)
unnamed: U4.7 (CEP), U4.9 (~PE), U4.10 (CET), U4.16 (VCC)
unnamed: U6.3 (C), U8.3
SC_0: U3.1 (AO), U4.14 (Q0)
SC_1: U3.2 (A1), U4.13 (Q1)
SC_2: U3.3 (A2), U4.12 (Q2)
SCr: U1.10
VCC: C1.1, SW1.1 (A), U3.6 (E3), U3.16 (Vcc), U5.16 (VCC), U6.4 (~S), U7.16 (VCC)
XTD: U6.2 (D), U8.2
XTD_INSTR: U6.5 (Q)
~CLK: U4.2 (CP)
~CLR: U2.2, U2.3
