michaelkamprath/eater-sap-1-improvements/instruction-register-8-bit/schematics/memory-map-controller/memory-map-controller.kicad_sch

## KiCad design instruction-register-8-bit/schematics/memory-map-controller/memory-map-controller.kicad_sch (2022-03-06)

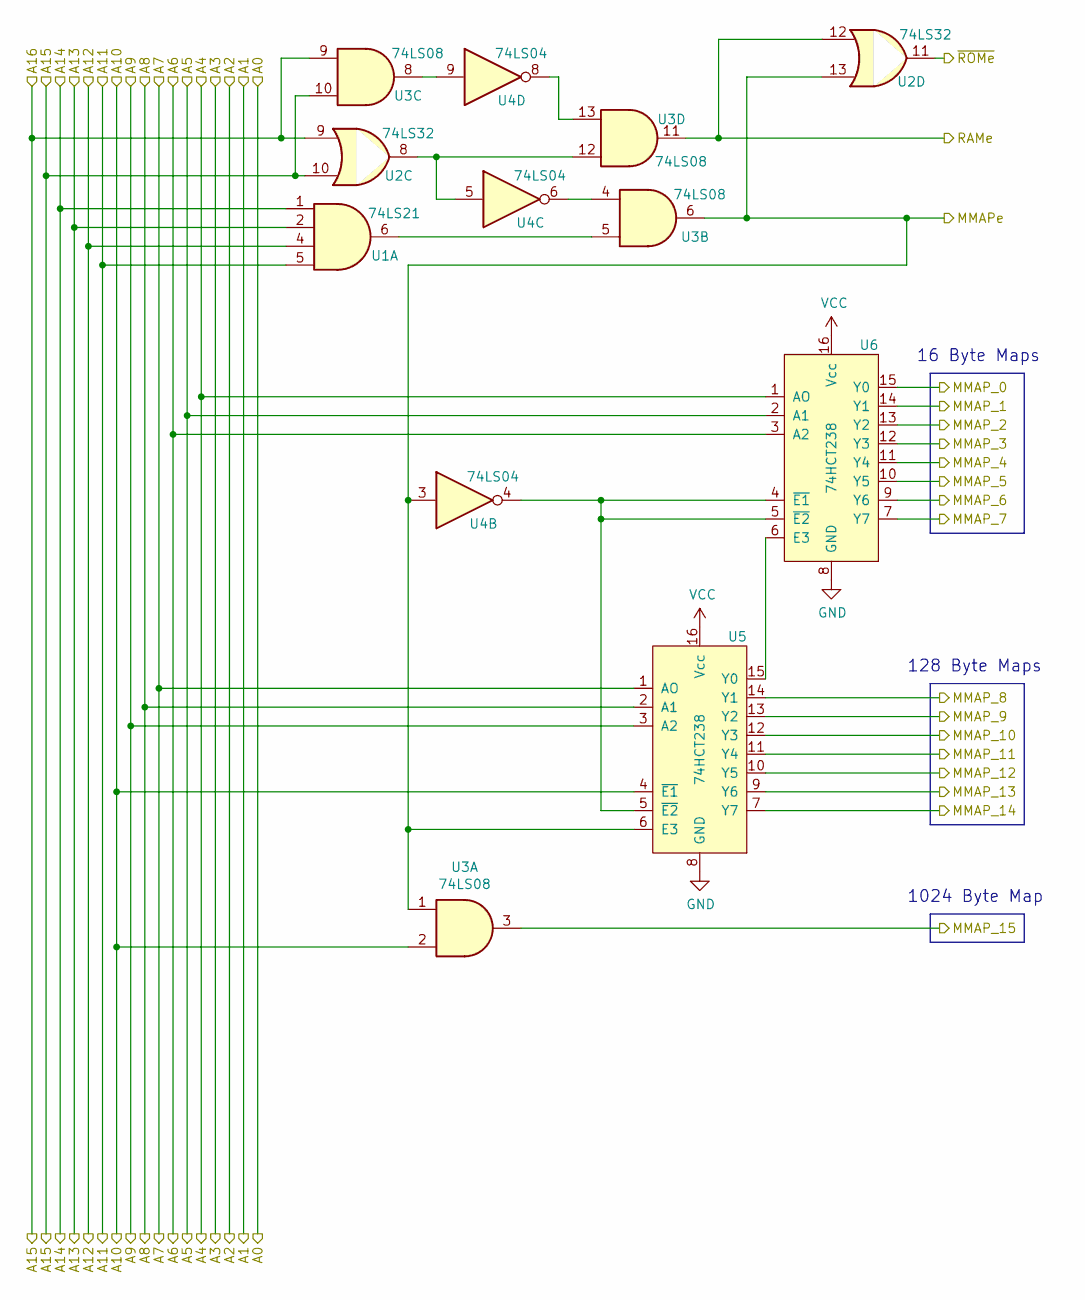
[picture p41: schematic memory-map-controller.kicad_sch]

Parts:
U1: 74LS21
U2: 74LS32
U3: 74LS08
U4: 74LS04
U5, U6: 74HCT238

Connections:
A4: U6.1 (AO)
A5: U6.2 (A1)
A6: U6.3 (A2)
A7: U5.1 (AO)
A8: U5.2 (A1)
A9: U5.3 (A2)
A10: U3.2, U5.4 (~E1)
A11: U1.5
A12: U1.4
A13: U1.2
A14: U1.1
A15: U2.9, U2.10, U3.9, U3.10
GND: U5.8 (GND), U6.8 (GND)
MMAP_0: U6.15 (Y0)
MMAP_1: U6.14 (Y1)
MMAP_2: U6.13 (Y2)
MMAP_3: U6.12 (Y3)
MMAP_4: U6.11 (Y4)
MMAP_5: U6.10 (Y5)
MMAP_6: U6.9 (Y6)
MMAP_7: U6.7 (Y7)
MMAP_8: U5.14 (Y1)
MMAP_9: U5.13 (Y2)
MMAP_10: U5.12 (Y3)
MMAP_11: U5.11 (Y4)
MMAP_12: U5.10 (Y5)
MMAP_13: U5.9 (Y6)
MMAP_14: U5.7 (Y7)
MMAP_15: U3.3
MMAPe: U2.13, U3.1, U3.6, U4.3, U5.6 (E3)
unnamed: U1.6, U3.5
unnamed: U2.8, U3.12, U4.5
unnamed: U3.4, U4.6
unnamed: U3.8, U4.9
unnamed: U3.13, U4.8
unnamed: U4.4, U5.5 (~E2), U6.4 (~E1), U6.5 (~E2)
unnamed: U5.15 (Y0), U6.6 (E3)
RAMe: U2.12, U3.11
VCC: U5.16 (Vcc), U6.16 (Vcc)
~ROMe: U2.11

Notes on the sheet:
128 Byte Maps
1024 Byte Map
16 Byte Maps
