michaelkamprath/eater-sap-1-improvements/lcd-display/schematics/clock-module-with-error-halt/clock-module-with-error-halt.kicad_sch

## KiCad design lcd-display/schematics/clock-module-with-error-halt/clock-module-with-error-halt.kicad_sch (2022-03-06)

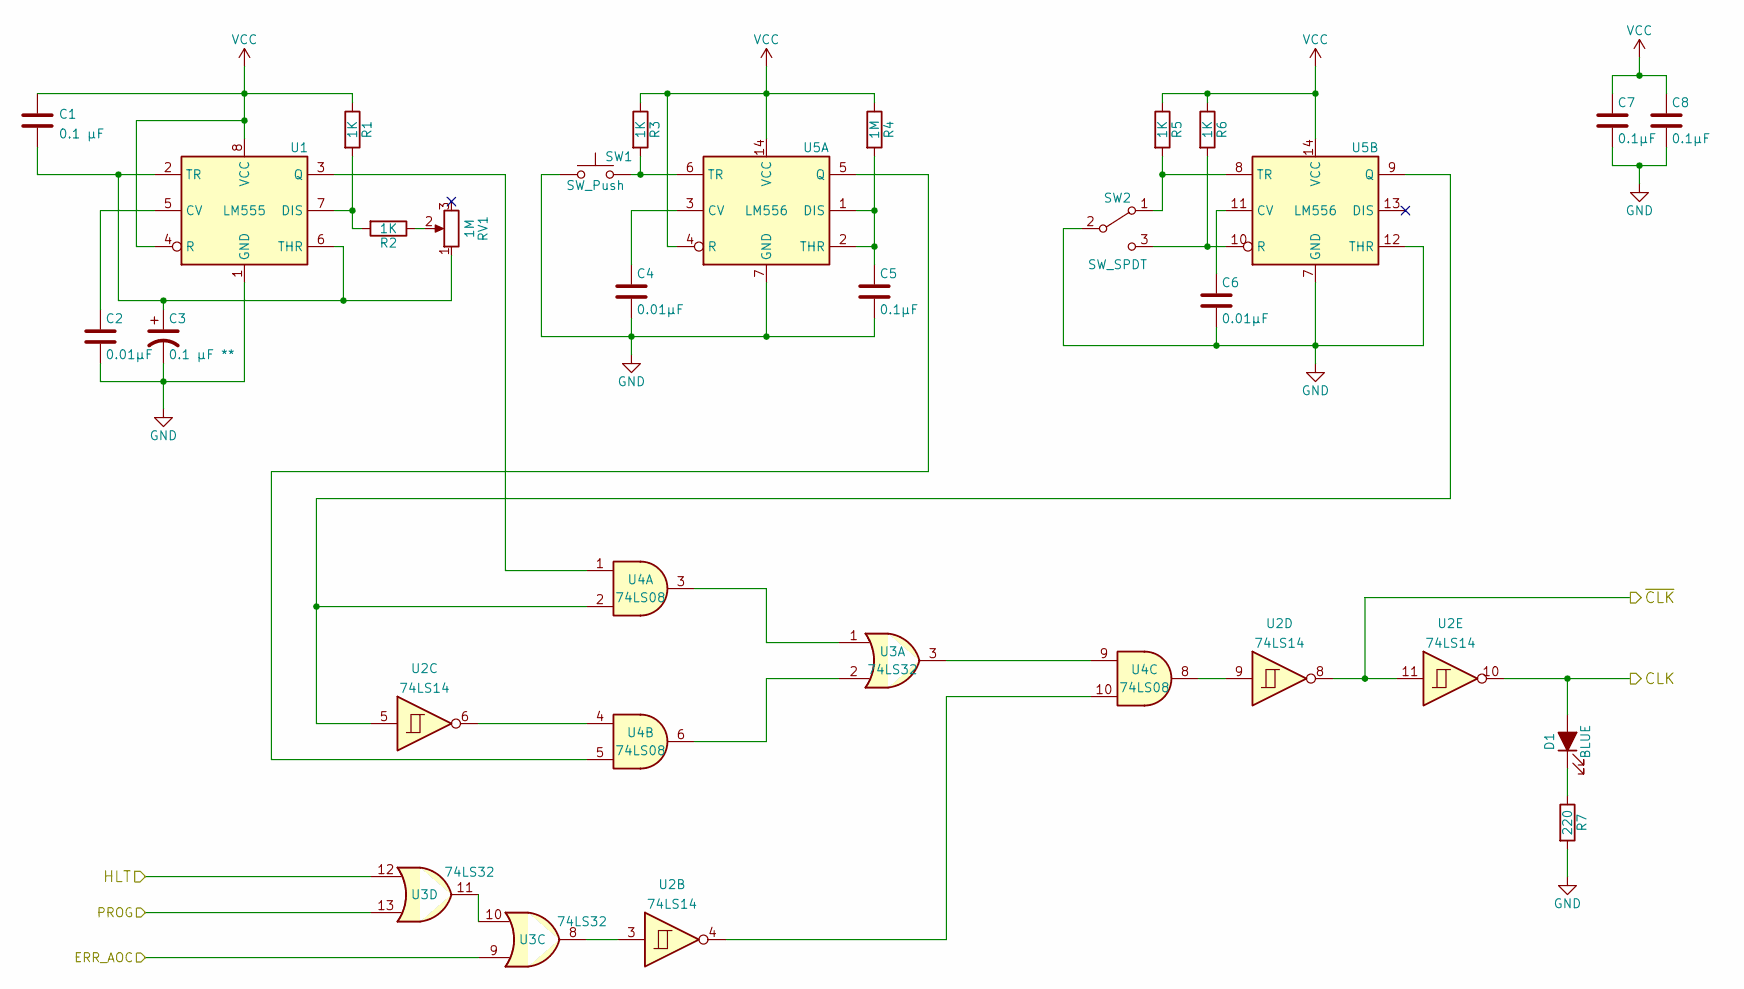
[picture p42: schematic clock-module-with-error-halt.kicad_sch]

Parts:
C1: 0.1 µF
C2, C4, C6: 0.01µF; C_Disc_D4.3mm_W1.9mm_P5.00mm
C3: 0.1 µF **; CP_Radial_D5.0mm_P2.00mm
C5, C7, C8: 0.1µF; C_Disc_D4.3mm_W1.9mm_P5.00mm
D1: BLUE; LED_D5.0mm
R1, R2, R3, R5, R6: 1K; R_Axial_DIN0207_L6.3mm_D2.5mm_P7.62mm_Horizontal
R4: 1M; R_Axial_DIN0207_L6.3mm_D2.5mm_P7.62mm_Horizontal
R7: 220; R_Axial_DIN0207_L6.3mm_D2.5mm_P7.62mm_Horizontal
RV1: 1M; Potentiometer-5.5mm
SW1: SW_Push; SW_PUSH_6mm_H5mm
SW2: SW_SPDT; DPDT-pushbutton
U1: LM555; DIP-8_W7.62mm
U2: 74LS14
U3: 74LS32; DIP-14_W7.62mm
U4: 74LS08; DIP-14_W7.62mm
U5: LM556

Connections:
CLK: D1.2 (A), U2.10
ERR_AOC: U3.9
GND: C2.2, C3.2, C4.2, C5.2, C6.2, C7.2, C8.2, R7.2, SW1.1, SW2.2 (B), U1.1 (GND), U5.7 (GND), U5.12 (THR)
HLT: U3.12
unnamed: C1.2, C3.1, RV1.1, U1.2 (TR), U1.6 (THR)
unnamed: C2.1, U1.5 (CV)
unnamed: C4.1, U5.3 (CV)
unnamed: C5.1, R4.2, U5.1 (DIS), U5.2 (THR)
unnamed: C6.1, U5.11 (CV)
unnamed: D1.1 (K), R7.1
unnamed: R1.2, R2.2, U1.7 (DIS)
unnamed: R2.1, RV1.2
unnamed: R3.2, SW1.2, U5.6 (TR)
unnamed: R5.2, SW2.1 (A), U5.8 (TR)
unnamed: R6.2, SW2.3 (C), U5.10 (R)
unnamed: U1.3 (Q), U4.1
unnamed: U2.3, U3.8
unnamed: U2.4, U4.10
unnamed: U2.5, U4.2, U5.9 (Q)
unnamed: U2.6, U4.4
unnamed: U2.9, U4.8
unnamed: U3.1, U4.3
unnamed: U3.2, U4.6
unnamed: U3.3, U4.9
unnamed: U3.10, U3.11
unnamed: U4.5, U5.5 (Q)
PROG: U3.13
VCC: C1.1, C7.1, C8.1, R1.1, R3.1, R4.1, R5.1, R6.1, U1.4 (R), U1.8 (VCC), U5.4 (R), U5.14 (VCC)
~CLK: U2.8, U2.11
