michaelkamprath/eater-sap-1-improvements/ram-rom-upgrade/schematics/clock-module-v2/clock-module-v2.sch

## KiCad design ram-rom-upgrade/schematics/clock-module-v2/clock-module-v2.sch (2021-07-11, an earlier design)

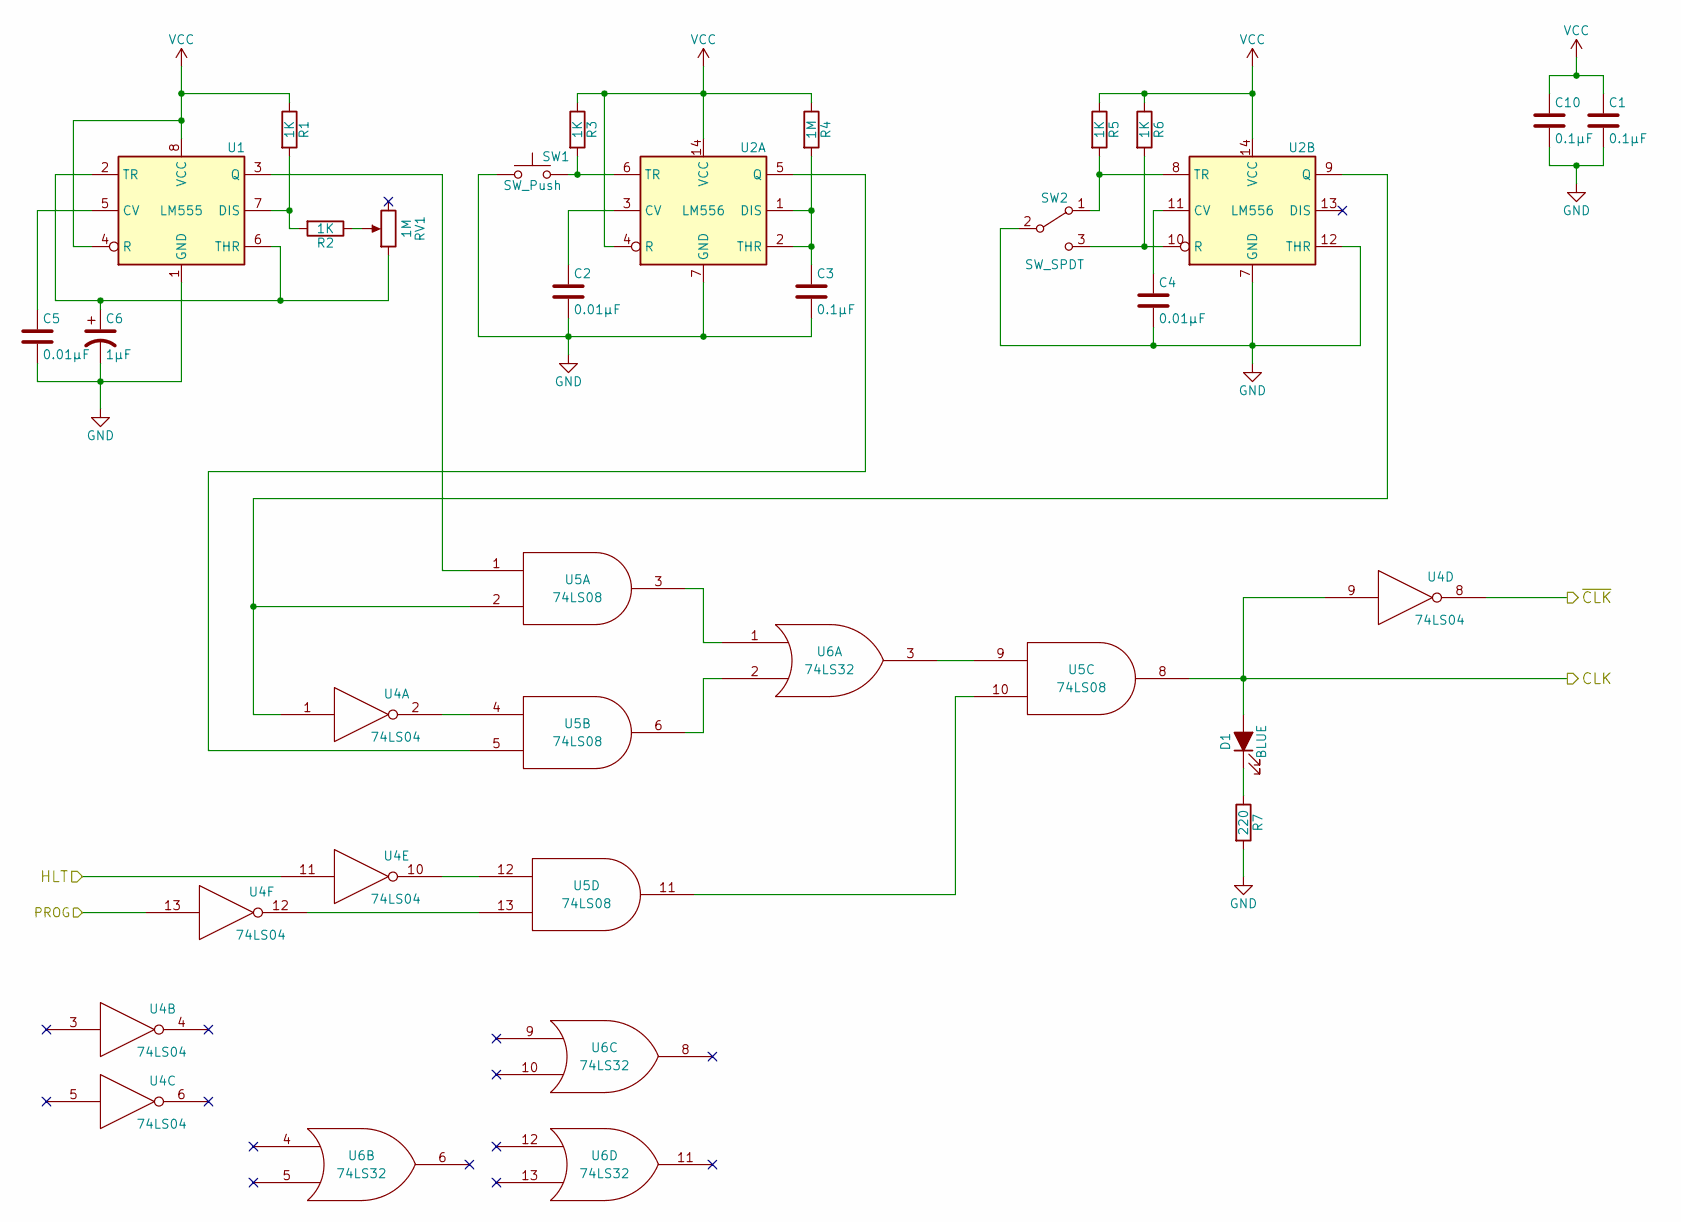
[picture p44: schematic clock-module-v2.sch]

Parts:
C1, C3, C10: 0.1µF; C_Disc_D4.3mm_W1.9mm_P5.00mm
C2, C4, C5: 0.01µF; C_Disc_D4.3mm_W1.9mm_P5.00mm
C6: 1µF; CP_Radial_D5.0mm_P2.00mm
D1: BLUE; LED_D5.0mm
R1, R2, R3, R5, R6: 1K; R_Axial_DIN0207_L6.3mm_D2.5mm_P7.62mm_Horizontal
R4: 1M; R_Axial_DIN0207_L6.3mm_D2.5mm_P7.62mm_Horizontal
R7: 220; R_Axial_DIN0207_L6.3mm_D2.5mm_P7.62mm_Horizontal
RV1: 1M; Potentiometer-5.5mm
SW1: SW_Push; SW_PUSH_6mm_H5mm
SW2: SW_SPDT; DPDT-pushbutton
U1: LM555; DIP-8_W7.62mm
U2: LM556
U4: 74LS04; DIP-14_W7.62mm
U5: 74LS08; DIP-14_W7.62mm
U6: 74LS32; DIP-14_W7.62mm

Connections:
CLK: D1.2 (A), U4.9, U5.8
GND: C1.2, C2.2, C3.2, C4.2, C5.2, C6.2, C10.2, R7.2, SW1.1, SW2.2 (B), U1.1 (GND), U2.7 (GND), U2.12 (THR)
HLT: U4.11
unnamed: C2.1, U2.3 (CV)
unnamed: C3.1, R4.2, U2.1 (DIS), U2.2 (THR)
unnamed: C4.1, U2.11 (CV)
unnamed: C5.1, U1.5 (CV)
unnamed: C6.1, RV1.1, U1.2 (TR), U1.6 (THR)
unnamed: D1.1 (K), R7.1
unnamed: R1.2, R2.2, U1.7 (DIS)
unnamed: R2.1, RV1.2
unnamed: R3.2, SW1.2, U2.6 (TR)
unnamed: R5.2, SW2.1 (A), U2.8 (TR)
unnamed: R6.2, SW2.3 (C), U2.10 (R)
unnamed: U1.3 (Q), U5.1
unnamed: U2.5 (Q), U5.5
unnamed: U2.9 (Q), U4.1, U5.2
unnamed: U4.2, U5.4
unnamed: U4.10, U5.12
unnamed: U4.12, U5.13
unnamed: U5.3, U6.1
unnamed: U5.6, U6.2
unnamed: U5.9, U6.3
unnamed: U5.10, U5.11
PROG: U4.13
VCC: C1.1, C10.1, R1.1, R3.1, R4.1, R5.1, R6.1, U1.4 (R), U1.8 (VCC), U2.4 (R), U2.14 (VCC)
~CLK: U4.8
