michaelkamprath/eater-sap-1-improvements/improving-reliability-of-ram-module/ram-module/ram-module.sch

## KiCad design improving-reliability-of-ram-module/ram-module/ram-module.sch (2020-12-26)

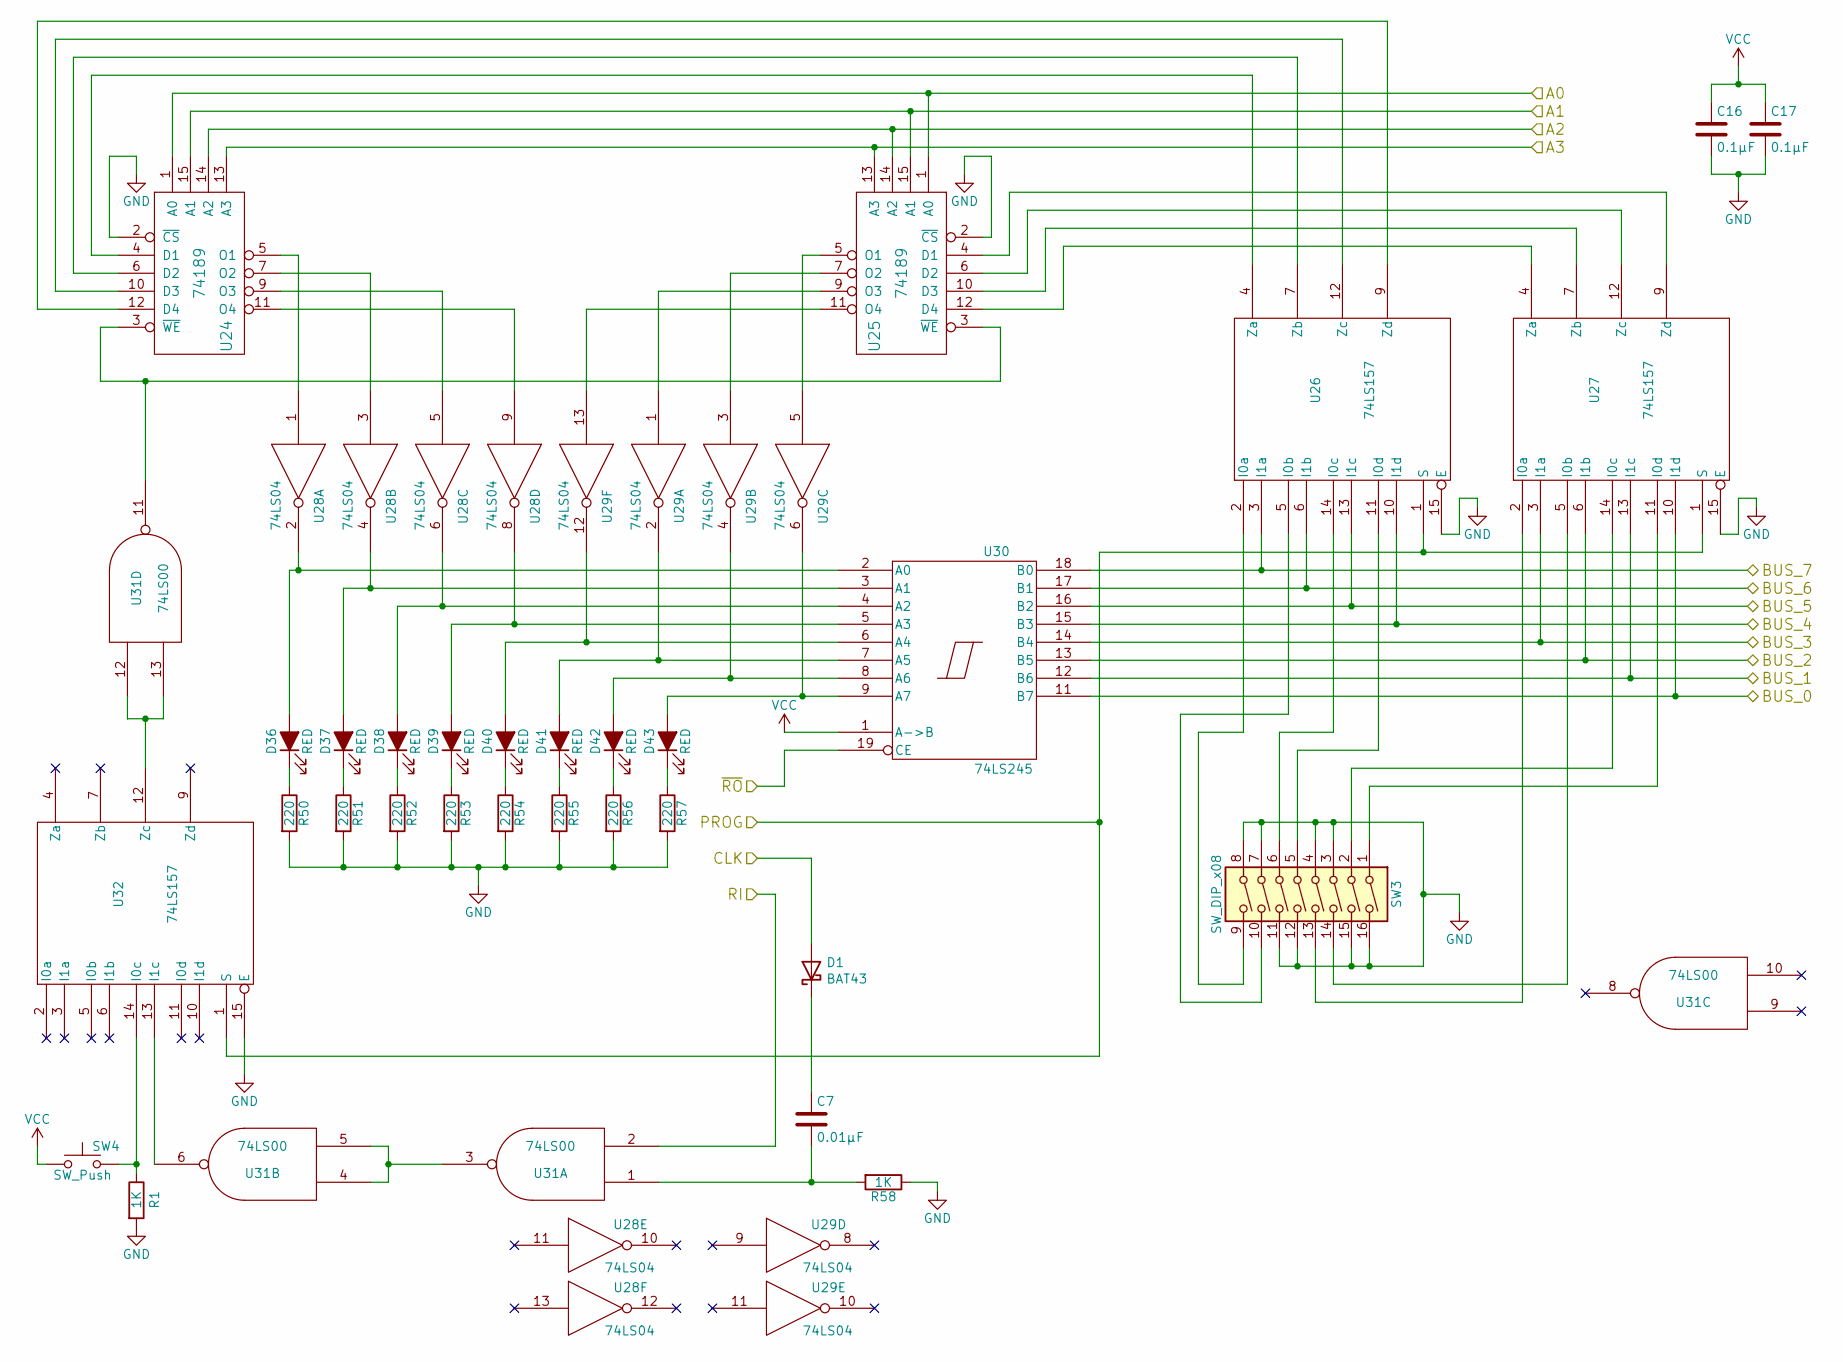
[picture p48: schematic ram-module.sch]

Parts:
C7: 0.01µF; C_Disc_D4.3mm_W1.9mm_P5.00mm
C16, C17: 0.1µF; C_Disc_D4.3mm_W1.9mm_P5.00mm
D1: BAT43
D36, D37, D38, D39, D40, D41, D42, D43: RED; LED_D5.0mm
R1: 1K
R50, R51, R52, R53, R54, R55, R56, R57: 220; R_Axial_DIN0207_L6.3mm_D2.5mm_P7.62mm_Horizontal
R58: 1K; R_Axial_DIN0207_L6.3mm_D2.5mm_P7.62mm_Horizontal
SW3: SW_DIP_x08; SW_DIP_SPSTx08_Slide_9.78x22.5mm_W7.62mm_P2.54mm
SW4: SW_Push; SW_PUSH_6mm_H5mm
U24, U25: 74189; DIP-16_W7.62mm
U26, U27, U32: 74LS157; DIP-16_W7.62mm
U28, U29: 74LS04; DIP-14_W7.62mm
U30: 74LS245; DIP-20_W7.62mm
U31: 74LS00; DIP-14_W7.62mm

Connections:
A0: U24.1 (A0), U25.1 (A0)
A1: U24.15 (A1), U25.15 (A1)
A2: U24.14 (A2), U25.14 (A2)
A3: U24.13 (A3), U25.13 (A3)
BUS_0: U27.10 (I1d), U30.11 (B7)
BUS_1: U27.13 (I1c), U30.12 (B6)
BUS_2: U27.6 (I1b), U30.13 (B5)
BUS_3: U27.3 (I1a), U30.14 (B4)
BUS_4: U26.10 (I1d), U30.15 (B3)
BUS_5: U26.13 (I1c), U30.16 (B2)
BUS_6: U26.6 (I1b), U30.17 (B1)
BUS_7: U26.3 (I1a), U30.18 (B0)
CLK: D1.2 (A)
GND: C16.2, C17.2, R1.2, R50.2, R51.2, R52.2, R53.2, R54.2, R55.2, R56.2, R57.2, R58.1, SW3.3, SW3.4, SW3.7, SW3.8, SW3.11, SW3.12, SW3.15, SW3.16, U24.2 (~CS), U25.2 (~CS), U26.15 (E), U27.15 (E), U32.15 (E)
unnamed: C7.1, D1.1 (K)
unnamed: C7.2, R58.2, U31.1
unnamed: D36.1 (K), R50.1
unnamed: D36.2 (A), U28.2, U30.2 (A0)
unnamed: D37.1 (K), R51.1
unnamed: D37.2 (A), U28.4, U30.3 (A1)
unnamed: D38.1 (K), R52.1
unnamed: D38.2 (A), U28.6, U30.4 (A2)
unnamed: D39.1 (K), R53.1
unnamed: D39.2 (A), U28.8, U30.5 (A3)
unnamed: D40.1 (K), R54.1
unnamed: D40.2 (A), U29.12, U30.6 (A4)
unnamed: D41.1 (K), R55.1
unnamed: D41.2 (A), U29.2, U30.7 (A5)
unnamed: D42.1 (K), R56.1
unnamed: D42.2 (A), U29.4, U30.8 (A6)
unnamed: D43.1 (K), R57.1
unnamed: D43.2 (A), U29.6, U30.9 (A7)
unnamed: R1.1, SW4.2, U32.14 (I0c)
unnamed: SW3.1, U27.11 (I0d)
unnamed: SW3.2, U27.14 (I0c)
unnamed: SW3.5, U26.11 (I0d)
unnamed: SW3.6, U26.14 (I0c)
unnamed: SW3.9, U26.2 (I0a)
unnamed: SW3.10, U26.5 (I0b)
unnamed: SW3.13, U27.2 (I0a)
unnamed: SW3.14, U27.5 (I0b)
unnamed: U24.3 (~WE), U25.3 (~WE), U31.11
unnamed: U24.4 (D1), U26.4 (Za)
unnamed: U24.5 (O1), U28.1
unnamed: U24.6 (D2), U26.7 (Zb)
unnamed: U24.7 (O2), U28.3
unnamed: U24.9 (O3), U28.5
unnamed: U24.10 (D3), U26.12 (Zc)
unnamed: U24.11 (O4), U28.9
unnamed: U24.12 (D4), U26.9 (Zd)
unnamed: U25.4 (D1), U27.9 (Zd)
unnamed: U25.5 (O1), U29.5
unnamed: U25.6 (D2), U27.12 (Zc)
unnamed: U25.7 (O2), U29.3
unnamed: U25.9 (O3), U29.1
unnamed: U25.10 (D3), U27.7 (Zb)
unnamed: U25.11 (O4), U29.13
unnamed: U25.12 (D4), U27.4 (Za)
unnamed: U31.3, U31.4, U31.5
unnamed: U31.6, U32.13 (I1c)
unnamed: U31.12, U31.13, U32.12 (Zc)
PROG: U26.1 (S), U27.1 (S), U32.1 (S)
RI: U31.2
VCC: C16.1, C17.1, SW4.1, U30.1 (A->B)
~RO: U30.19 (CE)
